azrang/Switch-Mode-Power-Supply/Testing Materials/Images/buck_10khz_50duty_1.png

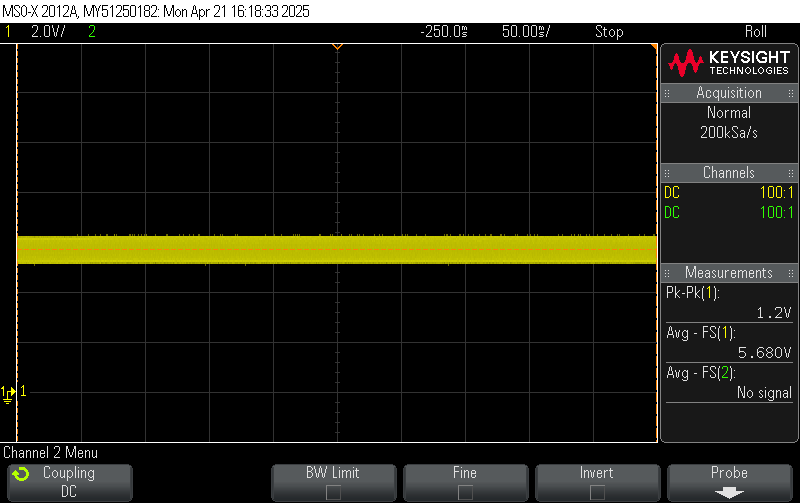
Testing Materials/Images/buck_10khz_50duty_1.png
