azrang/Switch-Mode-Power-Supply/Testing Materials/Images/flyouta_pwm_sweep2.bmp

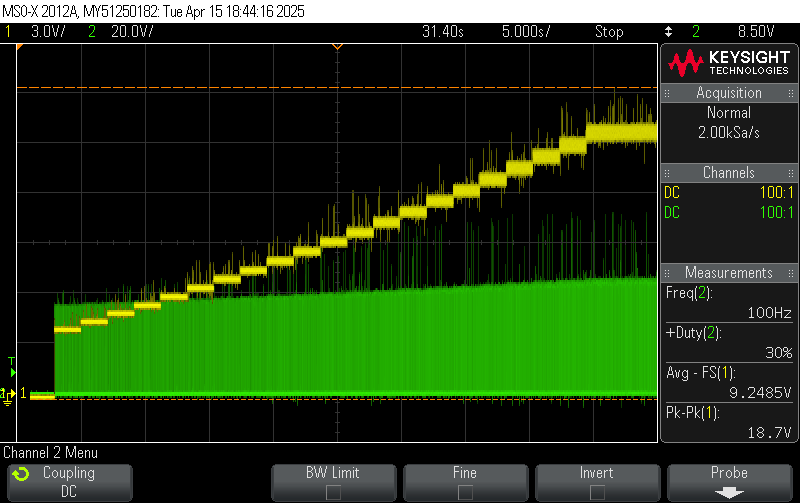
Testing Materials/Images/flyouta_pwm_sweep2.bmp
