azrang/Switch-Mode-Power-Supply/Testing Materials/Images/flyouta_pwm_sweep3.bmp

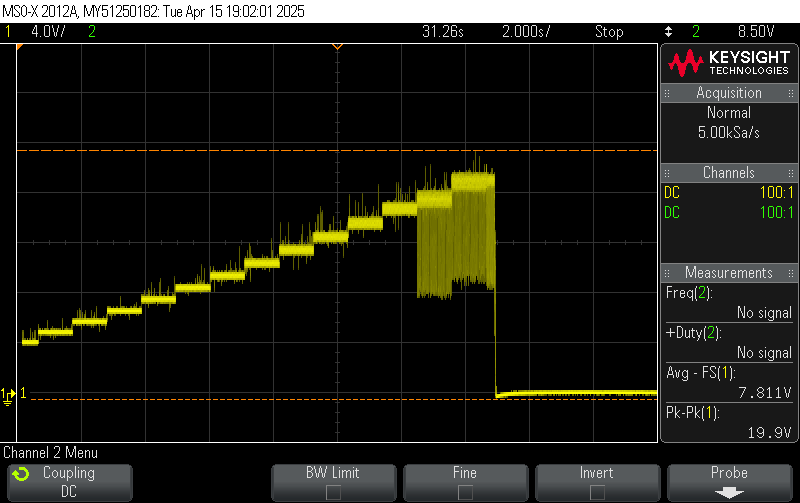
Testing Materials/Images/flyouta_pwm_sweep3.bmp
