azrang/Switch-Mode-Power-Supply/Testing Materials/Images/flyouta_pwm_sweep16.png

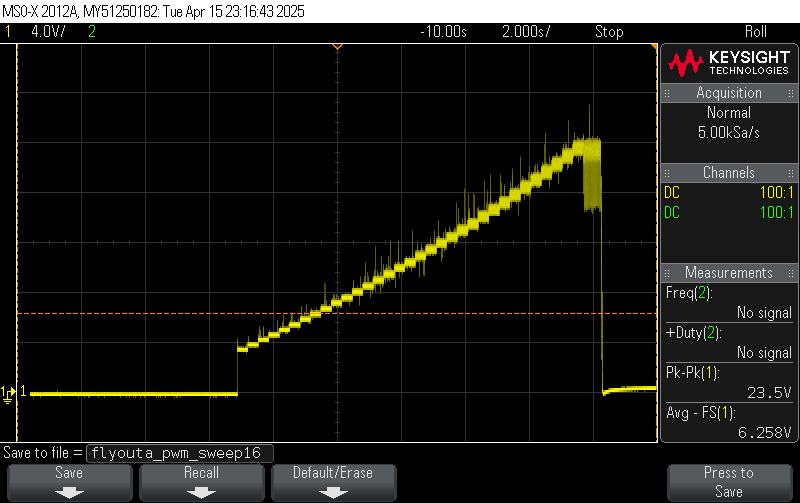
Testing Materials/Images/flyouta_pwm_sweep16.png
