azrang/Switch-Mode-Power-Supply/Testing Materials/Images/flyouta_pwm_sweep17.png

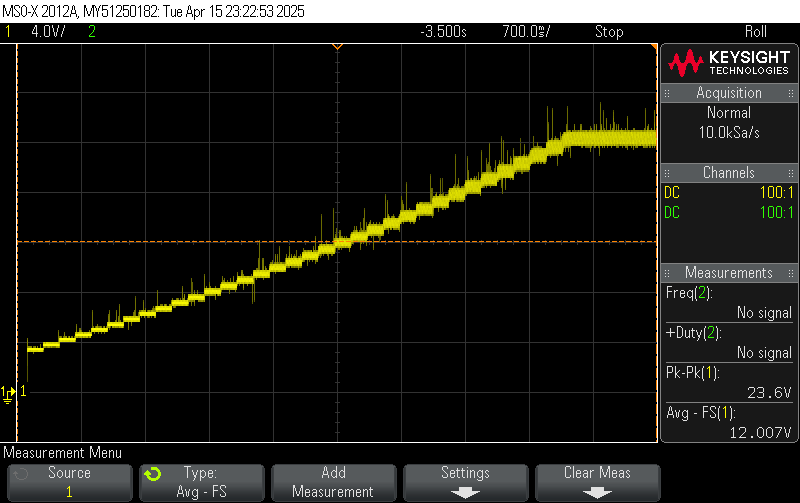
Testing Materials/Images/flyouta_pwm_sweep17.png
