azrang/Switch-Mode-Power-Supply/LTSpice Simulations/Buck Converter/Buck_Converter.asc

C1: cap; 10µ
C2: cap; 10µ
D1: schottky; MBR20100CT
L1: ind; 680µ
L2: ind; 680µ
M1: nmos; IRLHM630
M2: nmos; IRLHM630
M3: nmos; IRLHM630
R1: res; 1k
R2: res; 1k
R3: res; 1k
RLoad1: res; 100
RLoad: res; 100
U1: BSS138_ZTX
U2: BSS138_ZTX
U3: BSS138_ZTX
V1: voltage; 12
V2: voltage; PULSE(0 3.3 0 1n 1n {D*100u} 100u)
V3: voltage; 3.3
Named nets: MCU_PWM, VIN, 0, PWM2, VOUT2, SW2, PWM, 3V3, nPWM2, VOUT1, SW1
.tran 0.5
Higher inductor value limits peak current output, peak
voltage output, and slows down system.
.param D=0.95
PWM follows MCU input at Vin logic level
Need to test it at various loads:
- No load     (failed)
- 100 Ohm   (good)
- 1kOhm      (good)
- 10kOhm    (good)
- 100kOhm  (good)
 
They work, but PWM is dependent on the resistance.
Higher the resistance, lower the duty cycle needed
for higher voltages. All resistances can output 1V - 10V
however. Thus, feedback circuit is mandatory.
 
Lower Duty Cycle Bound: 10%
Upper Duty Cycle Bound: 95%
Pull up can't be too high
because tau = R*C and
takes too long for PWM 
peak to charge at low 
duty cycle. Need 1k or else
power burned is too much.
Buck Converter
D
G
S
D
G
S
nPWM2 is inverse
logic level
PWM2 follows
logic level
Higher capacitance increases
peak current output, peak 
voltage output, and slows
down system.
Asynchronous Buck Converter
Synchronous Buck Converter
Synchronous is more efficient at lower duty cycles.
DC @ 0.1 --> Async ==> 0.853V, Sync ==> 1.03V
Sync also had more ripples.
 
There seems to be little difference between sync & aysnc.
DC @ 0.93 --> Async ==> 10.25V, Sync ==> 10.21V
Sync has more ripples, however.
 
Therefore, will be using synchronous design.
 
Power consumption is also an issue, so need a greater
resistance, so sync design is not viable.
Target voltage range: 1V - 10V
Logical Level Shift 2
Logical Level Shift 1
.inc BSS138.spice.txt
