azrang/Switch-Mode-Power-Supply/LTSpice Simulations/OVP/OVP.asc

D2: zener; KDZV20B
Q1: pnp; FMMT718
Q2: pnp; FMMT718
Q3: pnp; DSS5540X
Q5: pnp; DSS5540X
R1: res; 1.5
R2: res; 300
R3: res; 1k
R4: res; 1k
R5: res; 7
R6: res; 1.2k
R7: res; 3k
R8: res; 2.7k
U1: DI_BZX84C5V6
V1: voltage; SINE(3 3 1k)
V2: voltage; 21
Named nets: 0
.inc FMMT718Q.txt
.tran 5m
.inc BZX84C5V6.txt
.inc kdzv20b.lib
Clipping at 5.75V
Over Voltage Protection
Clipping at 21.6V
.inc Transistors.txt
