azrang/Switch-Mode-Power-Supply/LTSpice Simulations/feedback/sproj feedback buffer.asc

R1: res; 100k
R2: res; 525k
R3: res; 320k
R4: res; 180k
U1: OPAx333
U2: OPAx333
V1: voltage; 5
V2: voltage; 20
V3: voltage; 5
V4: voltage; 5
Named nets: 0, VOUT
.tran .1m
important to find a rail-to-rail input/output to get up to 3.2V on Vs = 5V
