azrang/Switch-Mode-Power-Supply/LTSpice Simulations/Opto Isolator/Opto_Isolator.asc

Q1: pnp; 2N3906
Q2: npn; 2N3904
Q3: pnp; 2N3906
Q4: npn; 2N3904
R1: res; 5
R2: res; 10k
R3: res; 80k
R4: res; 5
R5: res; 1k
R6: res; 10k
R7: res; 80k
U1: CNR200
V1: voltage; 5
V2: voltage; 5
V3: voltage; SINE(1.65 1.65 1k)
Named nets: 0, A_5V, BC_5V, out, in
Simulating analog opto-isolator with external feedback
.tran 10m
.inc AvagoHCNR200_MOD.txt
Due to two different MCU grounds, the potentiometer output from MCU A
must go through an opto-isolator before being read by MCU B. For the 
readings to be linear, external feedback was used.
