azrang/Switch-Mode-Power-Supply/LTSpice Simulations/Logical Level Shift/Logical_Level_Shift.asc

R1: res; 1k
R2: res; 1k
R3: res; 10k
R4: res; 1k
U1: BSS138_ZTX
U2: BSS138_ZTX
U3: BSS138_ZTX
V1: voltage; 12
V2: voltage; PULSE(0 3.3 0 1n 1n {D*20u} 20u)
V3: voltage; 3.3
Named nets: MCU_PWM, HV, 0, nPWM2, PWM2, 3V3, PWM
.tran .1m
D
G
S
D
G
S
Level Shift Logic from 3.3V to 5V
nPWM2 is inverse
logic level
PWM2 follows
logic level
Logic Level
Increased VDD 
logic level
D
G
S
Logical Shift Follower
Logical Shift
Inverter and Follower
.param D=0.1
Pull up can't be too high because
tau = R*C and takes too long for
PWM peak to charge at low duty cycle
(especially for higher voltages).
