azrang/Switch-Mode-Power-Supply/Firmware/Test Scripts/Channel_A_ESP32_PWM.cpp

// MCU Testing Script - Channel A ESP32
// Channel_A_ESP32_PWM.cpp
// Switch Mode Power Supply - Senior Projects
// Azra Rangwala, Ilona Lameka, Ridwan Hussain

#include <Arduino.h>

const int BUCK = 25; // MCU_A_GPIO25

int PWM = 102; // 10% Duty Cycle
int prevState = 0;

void setup() 
{
  ledcSetup(0, 10000, 10); // 10kHz, 10 bit resolution
  ledcAttachPin(BUCK, 0);
}

void loop() 
{
  if (!prevState)
  {
    ledcWrite(0, PWM);
    prevState = 1;
  }
}
